AloeVeraZ/TrainUI/Train UI Mini/TrainUIMiniCode/SubwayCatalog.h

#pragma once

#include <Arduino.h>

namespace SubwayCatalog {
struct RouteDef { const char *id; const char *badge; const char *service; const char *feedUrl; const char *aliases; uint16_t stationStart; uint16_t stationCount; };
struct StationDef { const char *id; const char *name; const char *borough; const char *northStop; const char *northLabel; const char *southStop; const char *southLabel; };

static const StationDef STATIONS[] = {
  {"119","103 St","Manhattan","119N","Uptown","119S","Downtown"},
  {"117","116 St-Columbia University","Manhattan","117N","Uptown","117S","Downtown"},
  {"116","125 St","Manhattan","116N","Uptown","116S","Downtown"},
  {"115","137 St-City College","Manhattan","115N","Uptown","115S","Downtown"},
  {"132","14 St","Manhattan","132N","Uptown","132S","Downtown"},
  {"114","145 St","Manhattan","114N","Uptown","114S","Downtown"},
  {"113","157 St","Manhattan","113N","Uptown","113S","Downtown"},
  {"112","168 St-Washington Hts","Manhattan","112N","Uptown","112S","Downtown"},
  {"131","18 St","Manhattan","131N","Uptown","131S","Downtown"},
  {"111","181 St","Manhattan","111N","The Bronx","111S","Downtown"},
  {"110","191 St","Manhattan","110N","The Bronx","110S","Downtown"},
  {"108","207 St","Manhattan","108N","The Bronx","108S","Downtown"},
  {"107","215 St","Manhattan","107N","The Bronx","107S","Downtown"},
  {"130","23 St","Manhattan","130N","Uptown","130S","Downtown"},
  {"104","231 St","Bronx","104N","Van Cortlandt","104S","Manhattan"},
  {"103","238 St","Bronx","103N","Van Cortlandt","103S","Manhattan"},
  {"129","28 St","Manhattan","129N","Uptown","129S","Downtown"},
  {"128","34 St-Penn Station","Manhattan","128N","Uptown","128S","Downtown"},
  {"126","50 St","Manhattan","126N","Uptown","126S","Downtown"},
  {"125","59 St-Columbus Circle","Manhattan","125N","Uptown","125S","Downtown"},
  {"124","66 St-Lincoln Center","Manhattan","124N","Uptown","124S","Downtown"},
  {"123","72 St","Manhattan","123N","Uptown","123S","Downtown"},
  {"122","79 St","Manhattan","122N","Uptown","122S","Downtown"},
  {"121","86 St","Manhattan","121N","Uptown","121S","Downtown"},
  {"120","96 St","Manhattan","120N","Uptown","120S","Downtown"},
  {"135","Canal St","Manhattan","135N","Uptown","135S","Downtown"},
  {"118","Cathedral Pkwy (110 St)","Manhattan","118N","Uptown","118S","Downtown"},
  {"137","Chambers St","Manhattan","137N","Uptown","137S","Downtown"},
  {"133","Christopher St-Stonewall","Manhattan","133N","Uptown","133S","Downtown"},
  {"109","Dyckman St","Manhattan","109N","The Bronx","109S","Downtown"},
  {"136","Franklin St","Manhattan","136N","Uptown","136S","Downtown"},
  {"134","Houston St","Manhattan","134N","Uptown","134S","Downtown"},
  {"106","Marble Hill-225 St","Manhattan","106N","The Bronx","106S","Downtown"},
  {"139","Rector St","Manhattan","139N","Uptown","139S","Downtown"},
  {"142","South Ferry","Manhattan","142N","Uptown","142S","South Ferry"},
  {"127","Times Sq-42 St","Manhattan","127N","Uptown","127S","Downtown"},
  {"101","Van Cortlandt Park-242 St","Bronx","101N","Van Cortlandt Park-242 St","101S","Manhattan"},
  {"138","WTC Cortlandt","Manhattan","138N","Uptown","138S","Downtown"},
  {"227","110 St-Malcolm X Plaza","Manhattan","227N","Uptown","227S","Downtown"},
  {"226","116 St","Manhattan","226N","Uptown","226S","Downtown"},
  {"225","125 St","Manhattan","225N","Uptown","225S","Downtown"},
  {"224","135 St","Manhattan","224N","Uptown","224S","Downtown"},
  {"132","14 St","Manhattan","132N","Uptown","132S","Downtown"},
  {"222","149 St-Hostos","Bronx","222N","Northbound","222S","Manhattan"},
  {"215","174 St","Bronx","215N","Northbound","215S","Manhattan"},
  {"131","18 St","Manhattan","131N","Uptown","131S","Downtown"},
  {"207","219 St","Bronx","207N","Northbound","207S","Manhattan"},
  {"206","225 St","Bronx","206N","Northbound","206S","Manhattan"},
  {"130","23 St","Manhattan","130N","Uptown","130S","Downtown"},
  {"205","233 St","Bronx","205N","Northbound","205S","Manhattan"},
  {"129","28 St","Manhattan","129N","Uptown","129S","Downtown"},
  {"221","3 Av-149 St","Bronx","221N","Northbound","221S","Manhattan"},
  {"128","34 St-Penn Station","Manhattan","128N","Uptown","128S","Downtown"},
  {"126","50 St","Manhattan","126N","Uptown","126S","Downtown"},
  {"125","59 St-Columbus Circle","Manhattan","125N","Uptown","125S","Downtown"},
  {"124","66 St-Lincoln Center","Manhattan","124N","Uptown","124S","Downtown"},
  {"123","72 St","Manhattan","123N","Uptown","123S","Downtown"},
  {"122","79 St","Manhattan","122N","Uptown","122S","Downtown"},
  {"121","86 St","Manhattan","121N","Uptown","121S","Downtown"},
  {"120","96 St","Manhattan","120N","Uptown","120S","Downtown"},
  {"210","Allerton Av","Bronx","210N","Northbound","210S","Manhattan"},
  {"235","Atlantic Av-Barclays Ctr","Brooklyn","235N","Manhattan","235S","Outbound"},
  {"236","Bergen St","Brooklyn","236N","Manhattan","236S","Outbound"},
  {"245","Beverly Rd","Brooklyn","245N","Manhattan","245S","Flatbush"},
  {"232","Borough Hall","Brooklyn","232N","Manhattan","232S","Outbound"},
  {"212","Bronx Park East","Bronx","212N","Northbound","212S","Manhattan"},
  {"209","Burke Av","Bronx","209N","Northbound","209S","Manhattan"},
  {"135","Canal St","Manhattan","135N","Uptown","135S","Downtown"},
  {"137","Chambers St","Manhattan","137N","Uptown","137S","Downtown"},
  {"133","Christopher St-Stonewall","Manhattan","133N","Uptown","133S","Downtown"},
  {"244","Church Av","Brooklyn","244N","Manhattan","244S","Flatbush"},
  {"231","Clark St","Brooklyn","231N","Manhattan","231S","Outbound"},
  {"250","Crown Hts-Utica Av","Brooklyn","250N","Manhattan","250S","Outbound"},
  {"213","E 180 St","Bronx","213N","Northbound","213S","Manhattan"},
  {"238","Eastern Pkwy-Brooklyn Museum","Brooklyn","238N","Manhattan","238S","Outbound"},
  {"247","Flatbush Av-Brooklyn College","Brooklyn","247N","Manhattan","247S","Flatbush Av-Brooklyn College"},
  {"239","Franklin Av-Medgar Evers College","Brooklyn","239N","Manhattan","239S","Outbound"},
  {"136","Franklin St","Manhattan","136N","Uptown","136S","Downtown"},
  {"216","Freeman St","Bronx","216N","Northbound","216S","Manhattan"},
  {"229","Fulton St","Manhattan","229N","Uptown","229S","Brooklyn"},
  {"237","Grand Army Plaza","Brooklyn","237N","Manhattan","237S","Outbound"},
  {"208","Gun Hill Rd","Bronx","208N","Northbound","208S","Manhattan"},
  {"134","Houston St","Manhattan","134N","Uptown","134S","Downtown"},
  {"233","Hoyt St","Brooklyn","233N","Manhattan","233S","Outbound"},
  {"218","Intervale Av","Bronx","218N","Northbound","218S","Manhattan"},
  {"220","Jackson Av","Bronx","220N","Northbound","220S","Manhattan"},
  {"254","Junius St","Brooklyn","254N","Manhattan","254S","New Lots"},
  {"249","Kingston Av","Brooklyn","249N","Manhattan","249S","Outbound"},
  {"204","Nereid Av","Bronx","204N","Northbound","204S","Manhattan"},
  {"234","Nevins St","Brooklyn","234N","Manhattan","234S","Outbound"},
  {"257","New Lots Av","Brooklyn","257N","Manhattan","257S","New Lots Av"},
  {"246","Newkirk Av-Little Haiti","Brooklyn","246N","Manhattan","246S","Flatbush"},
  {"248","Nostrand Av","Brooklyn","248N","Manhattan","248S","Outbound"},
  {"228","Park Place","Manhattan","228N","Uptown","228S","Brooklyn"},
  {"211","Pelham Pkwy","Bronx","211N","Northbound","211S","Manhattan"},
  {"255","Pennsylvania Av","Brooklyn","255N","Manhattan","255S","New Lots"},
  {"241","President St-Medgar Evers College","Brooklyn","241N","Manhattan","241S","Flatbush"},
  {"219","Prospect Av","Bronx","219N","Northbound","219S","Manhattan"},
  {"253","Rockaway Av","Brooklyn","253N","Manhattan","253S","New Lots"},
  {"252","Saratoga Av","Brooklyn","252N","Manhattan","252S","New Lots"},
  {"217","Simpson St","Bronx","217N","Northbound","217S","Manhattan"},
  {"242","Sterling St","Brooklyn","242N","Manhattan","242S","Flatbush"},
  {"251","Sutter Av-Rutland Rd","Brooklyn","251N","Manhattan","251S","New Lots"},
  {"127","Times Sq-42 St","Manhattan","127N","Uptown","127S","Downtown"},
  {"256","Van Siclen Av","Brooklyn","256N","Manhattan","256S","New Lots"},
  {"201","Wakefield-241 St","Bronx","201N","Wakefield-241 St","201S","Manhattan"},
  {"230","Wall St","Manhattan","230N","Uptown","230S","Brooklyn"},
  {"214","West Farms Sq-E Tremont Av","Bronx","214N","Northbound","214S","Manhattan"},
  {"243","Winthrop St","Brooklyn","243N","Manhattan","243S","Flatbush"},
  {"227","110 St-Malcolm X Plaza","Manhattan","227N","Uptown","227S","Downtown"},
  {"226","116 St","Manhattan","226N","Uptown","226S","Downtown"},
  {"225","125 St","Manhattan","225N","Uptown","225S","Downtown"},
  {"224","135 St","Manhattan","224N","Uptown","224S","Downtown"},
  {"132","14 St","Manhattan","132N","Uptown","132S","Downtown"},
  {"302","145 St","Manhattan","302N","Harlem","302S","Downtown"},
  {"128","34 St-Penn Station","Manhattan","128N","Uptown","128S","Downtown"},
  {"123","72 St","Manhattan","123N","Uptown","123S","Downtown"},
  {"120","96 St","Manhattan","120N","Uptown","120S","Downtown"},
  {"235","Atlantic Av-Barclays Ctr","Brooklyn","235N","Manhattan","235S","Outbound"},
  {"236","Bergen St","Brooklyn","236N","Manhattan","236S","Outbound"},
  {"232","Borough Hall","Brooklyn","232N","Manhattan","232S","Outbound"},
  {"137","Chambers St","Manhattan","137N","Uptown","137S","Downtown"},
  {"231","Clark St","Brooklyn","231N","Manhattan","231S","Outbound"},
  {"250","Crown Hts-Utica Av","Brooklyn","250N","Manhattan","250S","Outbound"},
  {"238","Eastern Pkwy-Brooklyn Museum","Brooklyn","238N","Manhattan","238S","Outbound"},
  {"239","Franklin Av-Medgar Evers College","Brooklyn","239N","Manhattan","239S","Outbound"},
  {"229","Fulton St","Manhattan","229N","Uptown","229S","Brooklyn"},
  {"237","Grand Army Plaza","Brooklyn","237N","Manhattan","237S","Outbound"},
  {"301","Harlem-148 St","Manhattan","301N","Harlem-148 St","301S","Downtown"},
  {"233","Hoyt St","Brooklyn","233N","Manhattan","233S","Outbound"},
  {"254","Junius St","Brooklyn","254N","Manhattan","254S","New Lots"},
  {"249","Kingston Av","Brooklyn","249N","Manhattan","249S","Outbound"},
  {"234","Nevins St","Brooklyn","234N","Manhattan","234S","Outbound"},
  {"257","New Lots Av","Brooklyn","257N","Manhattan","257S","New Lots Av"},
  {"248","Nostrand Av","Brooklyn","248N","Manhattan","248S","Outbound"},
  {"228","Park Place","Manhattan","228N","Uptown","228S","Brooklyn"},
  {"255","Pennsylvania Av","Brooklyn","255N","Manhattan","255S","New Lots"},
  {"253","Rockaway Av","Brooklyn","253N","Manhattan","253S","New Lots"},
  {"252","Saratoga Av","Brooklyn","252N","Manhattan","252S","New Lots"},
  {"251","Sutter Av-Rutland Rd","Brooklyn","251N","Manhattan","251S","New Lots"},
  {"127","Times Sq-42 St","Manhattan","127N","Uptown","127S","Downtown"},
  {"256","Van Siclen Av","Brooklyn","256N","Manhattan","256S","New Lots"},
  {"230","Wall St","Manhattan","230N","Uptown","230S","Brooklyn"},
  {"624","103 St","Manhattan","624N","The Bronx","624S","Downtown"},
  {"623","110 St","Manhattan","623N","The Bronx","623S","Downtown"},
  {"622","116 St","Manhattan","622N","The Bronx","622S","Downtown"},
  {"621","125 St","Manhattan","621N","The Bronx","621S","Downtown"},
  {"416","138 St-Grand Concourse","Bronx","416N","Northbound","416S","Manhattan"},
  {"635","14 St-Union Sq","Manhattan","635N","Uptown","635S","Downtown"},
  {"415","149 St-Hostos","Bronx","415N","Northbound","415S","Manhattan"},
  {"414","161 St-Yankee Stadium","Bronx","414N","Northbound","414S","Manhattan"},
  {"413","167 St","Bronx","413N","Northbound","413S","Manhattan"},
  {"412","170 St","Bronx","412N","Northbound","412S","Manhattan"},
  {"410","176 St","Bronx","410N","Northbound","410S","Manhattan"},
  {"408","183 St","Bronx","408N","Northbound","408S","Manhattan"},
  {"634","23 St-Baruch College","Manhattan","634N","Uptown","634S","Downtown"},
  {"633","28 St","Manhattan","633N","Uptown","633S","Downtown"},
  {"632","33 St","Manhattan","632N","Uptown","632S","Downtown"},
  {"630","51 St","Manhattan","630N","Uptown","630S","Downtown"},
  {"629","59 St","Manhattan","629N","Uptown","629S","Downtown"},
  {"628","68 St-Hunter College","Manhattan","628N","Uptown","628S","Downtown"},
  {"627","77 St","Manhattan","627N","Uptown","627S","Downtown"},
  {"626","86 St","Manhattan","626N","Uptown","626S","Downtown"},
  {"625","96 St","Manhattan","625N","The Bronx","625S","Downtown"},
  {"636","Astor Pl","Manhattan","636N","Uptown","636S","Downtown"},
  {"235","Atlantic Av-Barclays Ctr","Brooklyn","235N","Manhattan","235S","Outbound"},
  {"405","Bedford Park Blvd-Lehman College","Bronx","405N","Northbound","405S","Manhattan"},
  {"236","Bergen St","Brooklyn","236N","Manhattan","236S","Outbound"},
  {"637","Bleecker St","Manhattan","637N","Uptown","637S","Downtown"},
  {"423","Borough Hall","Brooklyn","423N","Manhattan","423S","Outbound"},
  {"420","Bowling Green","Manhattan","420N","Uptown","420S","Downtown"},
  {"640","Brooklyn Bridge-City Hall","Manhattan","640N","Uptown","640S","Downtown"},
  {"409","Burnside Av","Bronx","409N","Northbound","409S","Manhattan"},
  {"639","Canal St","Manhattan","639N","Uptown","639S","Downtown"},
  {"250","Crown Hts-Utica Av","Brooklyn","250N","Manhattan","250S","Outbound"},
  {"238","Eastern Pkwy-Brooklyn Museum","Brooklyn","238N","Manhattan","238S","Outbound"},
  {"407","Fordham Rd","Bronx","407N","Northbound","407S","Manhattan"},
  {"239","Franklin Av-Medgar Evers College","Brooklyn","239N","Manhattan","239S","Outbound"},
  {"418","Fulton St","Manhattan","418N","Uptown","418S","Downtown"},
  {"237","Grand Army Plaza","Brooklyn","237N","Manhattan","237S","Outbound"},
  {"631","Grand Central-42 St","Manhattan","631N","Uptown","631S","Downtown"},
  {"254","Junius St","Brooklyn","254N","Manhattan","254S","New Lots"},
  {"406","Kingsbridge Rd","Bronx","406N","Northbound","406S","Manhattan"},
  {"249","Kingston Av","Brooklyn","249N","Manhattan","249S","Outbound"},
  {"402","Mosholu Pkwy","Bronx","402N","Woodlawn","402S","Manhattan"},
  {"411","Mt Eden Av","Bronx","411N","Northbound","411S","Manhattan"},
  {"234","Nevins St","Brooklyn","234N","Manhattan","234S","Outbound"},
  {"257","New Lots Av","Brooklyn","257N","Manhattan","257S","New Lots Av"},
  {"248","Nostrand Av","Brooklyn","248N","Manhattan","248S","Outbound"},
  {"255","Pennsylvania Av","Brooklyn","255N","Manhattan","255S","New Lots"},
  {"253","Rockaway Av","Brooklyn","253N","Manhattan","253S","New Lots"},
  {"252","Saratoga Av","Brooklyn","252N","Manhattan","252S","New Lots"},
  {"638","Spring St","Manhattan","638N","Uptown","638S","Downtown"},
  {"251","Sutter Av-Rutland Rd","Brooklyn","251N","Manhattan","251S","New Lots"},
  {"256","Van Siclen Av","Brooklyn","256N","Manhattan","256S","New Lots"},
  {"419","Wall St","Manhattan","419N","Uptown","419S","Downtown"},
  {"401","Woodlawn","Bronx","401N","Woodlawn","401S","Manhattan"},
  {"621","125 St","Manhattan","621N","The Bronx","621S","Downtown"},
  {"416","138 St-Grand Concourse","Bronx","416N","Northbound","416S","Manhattan"},
  {"635","14 St-Union Sq","Manhattan","635N","Uptown","635S","Downtown"},
  {"222","149 St-Hostos","Bronx","222N","Northbound","222S","Manhattan"},
  {"215","174 St","Bronx","215N","Northbound","215S","Manhattan"},
  {"207","219 St","Bronx","207N","Northbound","207S","Manhattan"},
  {"206","225 St","Bronx","206N","Northbound","206S","Manhattan"},
  {"205","233 St","Bronx","205N","Northbound","205S","Manhattan"},
  {"221","3 Av-149 St","Bronx","221N","Northbound","221S","Manhattan"},
  {"629","59 St","Manhattan","629N","Uptown","629S","Downtown"},
  {"626","86 St","Manhattan","626N","Uptown","626S","Downtown"},
  {"210","Allerton Av","Bronx","210N","Northbound","210S","Manhattan"},
  {"235","Atlantic Av-Barclays Ctr","Brooklyn","235N","Manhattan","235S","Outbound"},
  {"502","Baychester Av","Bronx","502N","Eastchester","502S","Manhattan"},
  {"245","Beverly Rd","Brooklyn","245N","Manhattan","245S","Flatbush"},
  {"423","Borough Hall","Brooklyn","423N","Manhattan","423S","Outbound"},
  {"420","Bowling Green","Manhattan","420N","Uptown","420S","Downtown"},
  {"212","Bronx Park East","Bronx","212N","Northbound","212S","Manhattan"},
  {"640","Brooklyn Bridge-City Hall","Manhattan","640N","Uptown","640S","Downtown"},
  {"209","Burke Av","Bronx","209N","Northbound","209S","Manhattan"},
  {"244","Church Av","Brooklyn","244N","Manhattan","244S","Flatbush"},
  {"250","Crown Hts-Utica Av","Brooklyn","250N","Manhattan","250S","Outbound"},
  {"213","E 180 St","Bronx","213N","Northbound","213S","Manhattan"},
  {"501","Eastchester-Dyre Av","Bronx","501N","Eastchester-Dyre Av","501S","Manhattan"},
  {"247","Flatbush Av-Brooklyn College","Brooklyn","247N","Manhattan","247S","Flatbush Av-Brooklyn College"},
  {"239","Franklin Av-Medgar Evers College","Brooklyn","239N","Manhattan","239S","Outbound"},
  {"216","Freeman St","Bronx","216N","Northbound","216S","Manhattan"},
  {"418","Fulton St","Manhattan","418N","Uptown","418S","Downtown"},
  {"631","Grand Central-42 St","Manhattan","631N","Uptown","631S","Downtown"},
  {"208","Gun Hill Rd","Bronx","208N","Northbound","208S","Manhattan"},
  {"503","Gun Hill Rd","Bronx","503N","Eastchester","503S","Manhattan"},
  {"218","Intervale Av","Bronx","218N","Northbound","218S","Manhattan"},
  {"220","Jackson Av","Bronx","220N","Northbound","220S","Manhattan"},
  {"254","Junius St","Brooklyn","254N","Manhattan","254S","New Lots"},
  {"249","Kingston Av","Brooklyn","249N","Manhattan","249S","Outbound"},
  {"505","Morris Park","Bronx","505N","Eastchester","505S","Manhattan"},
  {"204","Nereid Av","Bronx","204N","Northbound","204S","Manhattan"},
  {"234","Nevins St","Brooklyn","234N","Manhattan","234S","Outbound"},
  {"257","New Lots Av","Brooklyn","257N","Manhattan","257S","New Lots Av"},
  {"246","Newkirk Av-Little Haiti","Brooklyn","246N","Manhattan","246S","Flatbush"},
  {"248","Nostrand Av","Brooklyn","248N","Manhattan","248S","Outbound"},
  {"211","Pelham Pkwy","Bronx","211N","Northbound","211S","Manhattan"},
  {"504","Pelham Pkwy","Bronx","504N","Eastchester","504S","Manhattan"},
  {"255","Pennsylvania Av","Brooklyn","255N","Manhattan","255S","New Lots"},
  {"241","President St-Medgar Evers College","Brooklyn","241N","Manhattan","241S","Flatbush"},
  {"219","Prospect Av","Bronx","219N","Northbound","219S","Manhattan"},
  {"253","Rockaway Av","Brooklyn","253N","Manhattan","253S","New Lots"},
  {"252","Saratoga Av","Brooklyn","252N","Manhattan","252S","New Lots"},
  {"217","Simpson St","Bronx","217N","Northbound","217S","Manhattan"},
  {"242","Sterling St","Brooklyn","242N","Manhattan","242S","Flatbush"},
  {"251","Sutter Av-Rutland Rd","Brooklyn","251N","Manhattan","251S","New Lots"},
  {"256","Van Siclen Av","Brooklyn","256N","Manhattan","256S","New Lots"},
  {"419","Wall St","Manhattan","419N","Uptown","419S","Downtown"},
  {"214","West Farms Sq-E Tremont Av","Bronx","214N","Northbound","214S","Manhattan"},
  {"243","Winthrop St","Brooklyn","243N","Manhattan","243S","Flatbush"},
  {"624","103 St","Manhattan","624N","The Bronx","624S","Downtown"},
  {"623","110 St","Manhattan","623N","The Bronx","623S","Downtown"},
  {"622","116 St","Manhattan","622N","The Bronx","622S","Downtown"},
  {"621","125 St","Manhattan","621N","The Bronx","621S","Downtown"},
  {"635","14 St-Union Sq","Manhattan","635N","Uptown","635S","Downtown"},
  {"634","23 St-Baruch College","Manhattan","634N","Uptown","634S","Downtown"},
  {"633","28 St","Manhattan","633N","Uptown","633S","Downtown"},
  {"619","3 Av-138 St","Bronx","619N","Northbound","619S","Manhattan"},
  {"632","33 St","Manhattan","632N","Uptown","632S","Downtown"},
  {"630","51 St","Manhattan","630N","Uptown","630S","Downtown"},
  {"629","59 St","Manhattan","629N","Uptown","629S","Downtown"},
  {"628","68 St-Hunter College","Manhattan","628N","Uptown","628S","Downtown"},
  {"627","77 St","Manhattan","627N","Uptown","627S","Downtown"},
  {"626","86 St","Manhattan","626N","Uptown","626S","Downtown"},
  {"625","96 St","Manhattan","625N","The Bronx","625S","Downtown"},
  {"636","Astor Pl","Manhattan","636N","Uptown","636S","Downtown"},
  {"637","Bleecker St","Manhattan","637N","Uptown","637S","Downtown"},
  {"618","Brook Av","Bronx","618N","Northbound","618S","Manhattan"},
  {"640","Brooklyn Bridge-City Hall","Manhattan","640N","Uptown","640S","Downtown"},
  {"602","Buhre Av","Bronx","602N","Pelham Bay","602S","Manhattan"},
  {"639","Canal St","Manhattan","639N","Uptown","639S","Downtown"},
  {"607","Castle Hill Av","Bronx","607N","Pelham Bay","607S","Manhattan"},
  {"617","Cypress Av","Bronx","617N","Northbound","617S","Manhattan"},
  {"616","E 143 St-St Mary's St","Bronx","616N","Northbound","616S","Manhattan"},
  {"615","E 149 St","Bronx","615N","Northbound","615S","Manhattan"},
  {"611","Elder Av","Bronx","611N","Northbound","611S","Manhattan"},
  {"631","Grand Central-42 St","Manhattan","631N","Uptown","631S","Downtown"},
  {"613","Hunts Point Av","Bronx","613N","Northbound","613S","Manhattan"},
  {"614","Longwood Av","Bronx","614N","Northbound","614S","Manhattan"},
  {"603","Middletown Rd","Bronx","603N","Pelham Bay","603S","Manhattan"},
  {"610","Morrison Av-Soundview","Bronx","610N","Northbound","610S","Manhattan"},
  {"608","Parkchester","Bronx","608N","Northbound","608S","Manhattan"},
  {"601","Pelham Bay Park","Bronx","601N","Pelham Bay Park","601S","Manhattan"},
  {"638","Spring St","Manhattan","638N","Uptown","638S","Downtown"},
  {"609","St Lawrence Av","Bronx","609N","Northbound","609S","Manhattan"},
  {"604","Westchester Sq-E Tremont Av","Bronx","604N","Pelham Bay","604S","Manhattan"},
  {"612","Whitlock Av","Bronx","612N","Northbound","612S","Manhattan"},
  {"606","Zerega Av","Bronx","606N","Pelham Bay","606S","Manhattan"},
  {"706","103 St-Corona Plaza","Queens","706N","Outbound","706S","Manhattan"},
  {"705","111 St","Queens","705N","Outbound","705S","Manhattan"},
  {"716","33 St-Rawson St","Queens","716N","Outbound","716S","Manhattan"},
  {"726","34 St-Hudson Yards","Manhattan","726N","Flushing-Main St","726S","Queens"},
  {"715","40 St-Lowery St","Queens","715N","Outbound","715S","Manhattan"},
  {"714","46 St-Bliss St","Queens","714N","Outbound","714S","Manhattan"},
  {"724","5 Av","Manhattan","724N","Queens","724S","Hudson Yards"},
  {"713","52 St","Queens","713N","Outbound","713S","Manhattan"},
  {"712","61 St-Woodside","Queens","712N","Outbound","712S","Manhattan"},
  {"711","69 St","Queens","711N","Outbound","711S","Manhattan"},
  {"710","74 St-Broadway","Queens","710N","Outbound","710S","Manhattan"},
  {"709","82 St-Jackson Hts","Queens","709N","Outbound","709S","Manhattan"},
  {"708","90 St-Elmhurst Av","Queens","708N","Outbound","708S","Manhattan"},
  {"719","Court Sq","Queens","719N","Outbound","719S","Manhattan"},
  {"701","Flushing-Main St","Queens","701N","Flushing-Main St","701S","Manhattan"},
  {"723","Grand Central-42 St","Manhattan","723N","Queens","723S","Hudson Yards"},
  {"720","Hunters Point Av","Queens","720N","Outbound","720S","Manhattan"},
  {"707","Junction Blvd","Queens","707N","Outbound","707S","Manhattan"},
  {"702","Mets-Willets Point","Queens","702N","Outbound","702S","Manhattan"},
  {"718","Queensboro Plaza","Queens","718N","Outbound","718S","Manhattan"},
  {"725","Times Sq-42 St","Manhattan","725N","Queens","725S","Hudson Yards"},
  {"721","Vernon Blvd-Jackson Av","Queens","721N","Outbound","721S","Manhattan"},
  {"A18","103 St","Manhattan","A18N","Uptown","A18S","Downtown"},
  {"A63","104 St","Queens","A63N","Manhattan","A63S","Ozone Park"},
  {"A64","111 St","Queens","A64N","Manhattan","A64S","Ozone Park"},
  {"A16","116 St","Manhattan","A16N","Uptown","A16S","Downtown"},
  {"A15","125 St","Manhattan","A15N","Uptown","A15S","Downtown"},
  {"A14","135 St","Manhattan","A14N","Uptown","A14S","Downtown"},
  {"A31","14 St","Manhattan","A31N","Uptown","A31S","Downtown"},
  {"A12","145 St","Manhattan","A12N","Uptown","A12S","Downtown"},
  {"A11","155 St","Manhattan","A11N","Uptown","A11S","Downtown"},
  {"A10","163 St-Amsterdam Av","Manhattan","A10N","Uptown","A10S","Downtown"},
  {"A09","168 St","Manhattan","A09N","Uptown","A09S","Downtown"},
  {"A07","175 St","Manhattan","A07N","Uptown","A07S","Downtown"},
  {"A06","181 St","Manhattan","A06N","Uptown","A06S","Downtown"},
  {"A05","190 St","Manhattan","A05N","Uptown","A05S","Downtown"},
  {"A30","23 St","Manhattan","A30N","Uptown","A30S","Downtown"},
  {"A28","34 St-Penn Station","Manhattan","A28N","Uptown","A28S","Downtown"},
  {"A27","42 St-Port Authority Bus Terminal","Manhattan","A27N","Uptown","A27S","Downtown"},
  {"A25","50 St","Manhattan","A25N","Uptown","A25S","Downtown"},
  {"A24","59 St-Columbus Circle","Manhattan","A24N","Uptown","A24S","Downtown"},
  {"A22","72 St","Manhattan","A22N","Uptown","A22S","Downtown"},
  {"A59","80 St","Queens","A59N","Manhattan","A59S","Outbound"},
  {"A21","81 St-Museum of Natural History","Manhattan","A21N","Uptown","A21S","Downtown"},
  {"A20","86 St","Manhattan","A20N","Uptown","A20S","Downtown"},
  {"A60","88 St","Queens","A60N","Manhattan","A60S","Outbound"},
  {"A19","96 St","Manhattan","A19N","Uptown","A19S","Downtown"},
  {"H01","Aqueduct Racetrack","Queens","H01N","Manhattan","H01S","Rockaways"},
  {"H02","Aqueduct-N Conduit Av","Queens","H02N","Manhattan","H02S","Rockaways"},
  {"H14","Beach 105 St","Queens","H14N","Inbound","H14S","Rockaway Park"},
  {"H10","Beach 25 St","Queens","H10N","Manhattan","H10S","Far Rockaway"},
  {"H09","Beach 36 St","Queens","H09N","Manhattan","H09S","Far Rockaway"},
  {"H08","Beach 44 St","Queens","H08N","Manhattan","H08S","Far Rockaway"},
  {"H07","Beach 60 St","Queens","H07N","Manhattan","H07S","Far Rockaway"},
  {"H06","Beach 67 St","Queens","H06N","Manhattan","H06S","Far Rockaway"},
  {"H12","Beach 90 St","Queens","H12N","Inbound","H12S","Rockaway Park"},
  {"H13","Beach 98 St","Queens","H13N","Inbound","H13S","Rockaway Park"},
  {"H04","Broad Channel","Queens","H04N","Inbound","H04S","Rockaways"},
  {"A51","Broadway Junction","Brooklyn","A51N","Manhattan","A51S","Outbound"},
  {"A34","Canal St","Manhattan","A34N","Uptown","A34S","Downtown"},
  {"A17","Cathedral Pkwy (110 St)","Manhattan","A17N","Uptown","A17S","Downtown"},
  {"A36","Chambers St","Manhattan","A36N","Uptown","A36S","Brooklyn"},
  {"A44","Clinton-Washington Avs","Brooklyn","A44N","Manhattan","A44S","Outbound"},
  {"A03","Dyckman St","Manhattan","A03N","Uptown","A03S","Downtown"},
  {"A55","Euclid Av","Brooklyn","A55N","Manhattan","A55S","Queens"},
  {"H11","Far Rockaway-Mott Av","Queens","H11N","Manhattan","H11S","Far Rockaway-Mott Av"},
  {"A45","Franklin Av","Brooklyn","A45N","Manhattan","A45S","Outbound"},
  {"A38","Fulton St","Manhattan","A38N","Uptown","A38S","Brooklyn"},
  {"A57","Grant Av","Brooklyn","A57N","Manhattan","A57S","Queens"},
  {"A40","High St","Brooklyn","A40N","Manhattan","A40S","Outbound"},
  {"H03","Howard Beach-JFK Airport","Queens","H03N","Manhattan","H03S","Rockaways"},
  {"A42","Hoyt-Schermerhorn Sts","Brooklyn","A42N","Westbound","A42S","Queens"},
  {"A02","Inwood-207 St","Manhattan","A02N","Inwood-207 St","A02S","Downtown"},
  {"A41","Jay St-MetroTech","Brooklyn","A41N","Manhattan","A41S","Outbound"},
  {"A47","Kingston-Throop Avs","Brooklyn","A47N","Manhattan","A47S","Outbound"},
  {"A43","Lafayette Av","Brooklyn","A43N","Manhattan","A43S","Outbound"},
  {"A52","Liberty Av","Brooklyn","A52N","Manhattan","A52S","Outbound"},
  {"A46","Nostrand Av","Brooklyn","A46N","Manhattan","A46S","Outbound"},
  {"A65","Ozone Park-Lefferts Blvd","Queens","A65N","Manhattan","A65S","Ozone Park-Lefferts Blvd"},
  {"A49","Ralph Av","Brooklyn","A49N","Manhattan","A49S","Outbound"},
  {"A50","Rockaway Av","Brooklyn","A50N","Manhattan","A50S","Outbound"},
  {"A61","Rockaway Blvd","Queens","A61N","Manhattan","A61S","Outbound"},
  {"H15","Rockaway Park-Beach 116 St","Queens","H15N","Inbound","H15S","Rockaway Park-Beach 116 St"},
  {"A54","Shepherd Av","Brooklyn","A54N","Manhattan","A54S","Outbound"},
  {"A33","Spring St","Manhattan","A33N","Uptown","A33S","Downtown"},
  {"A48","Utica Av","Brooklyn","A48N","Manhattan","A48S","Outbound"},
  {"A53","Van Siclen Av","Brooklyn","A53N","Manhattan","A53S","Outbound"},
  {"A32","W 4 St-Wash Sq","Manhattan","A32N","Uptown","A32S","Downtown"},
  {"A18","103 St","Manhattan","A18N","Uptown","A18S","Downtown"},
  {"A16","116 St","Manhattan","A16N","Uptown","A16S","Downtown"},
  {"A15","125 St","Manhattan","A15N","Uptown","A15S","Downtown"},
  {"A14","135 St","Manhattan","A14N","Uptown","A14S","Downtown"},
  {"A31","14 St","Manhattan","A31N","Uptown","A31S","Downtown"},
  {"A12","145 St","Manhattan","A12N","Uptown","A12S","Downtown"},
  {"A11","155 St","Manhattan","A11N","Uptown","A11S","Downtown"},
  {"A10","163 St-Amsterdam Av","Manhattan","A10N","Uptown","A10S","Downtown"},
  {"A09","168 St","Manhattan","A09N","Uptown","A09S","Downtown"},
  {"A30","23 St","Manhattan","A30N","Uptown","A30S","Downtown"},
  {"A28","34 St-Penn Station","Manhattan","A28N","Uptown","A28S","Downtown"},
  {"A27","42 St-Port Authority Bus Terminal","Manhattan","A27N","Uptown","A27S","Downtown"},
  {"A25","50 St","Manhattan","A25N","Uptown","A25S","Downtown"},
  {"A24","59 St-Columbus Circle","Manhattan","A24N","Uptown","A24S","Downtown"},
  {"A22","72 St","Manhattan","A22N","Uptown","A22S","Downtown"},
  {"A21","81 St-Museum of Natural History","Manhattan","A21N","Uptown","A21S","Downtown"},
  {"A20","86 St","Manhattan","A20N","Uptown","A20S","Downtown"},
  {"A19","96 St","Manhattan","A19N","Uptown","A19S","Downtown"},
  {"A51","Broadway Junction","Brooklyn","A51N","Manhattan","A51S","Outbound"},
  {"A34","Canal St","Manhattan","A34N","Uptown","A34S","Downtown"},
  {"A17","Cathedral Pkwy (110 St)","Manhattan","A17N","Uptown","A17S","Downtown"},
  {"A36","Chambers St","Manhattan","A36N","Uptown","A36S","Brooklyn"},
  {"A44","Clinton-Washington Avs","Brooklyn","A44N","Manhattan","A44S","Outbound"},
  {"A55","Euclid Av","Brooklyn","A55N","Manhattan","A55S","Queens"},
  {"A45","Franklin Av","Brooklyn","A45N","Manhattan","A45S","Outbound"},
  {"A38","Fulton St","Manhattan","A38N","Uptown","A38S","Brooklyn"},
  {"A40","High St","Brooklyn","A40N","Manhattan","A40S","Outbound"},
  {"A42","Hoyt-Schermerhorn Sts","Brooklyn","A42N","Westbound","A42S","Queens"},
  {"A41","Jay St-MetroTech","Brooklyn","A41N","Manhattan","A41S","Outbound"},
  {"A47","Kingston-Throop Avs","Brooklyn","A47N","Manhattan","A47S","Outbound"},
  {"A43","Lafayette Av","Brooklyn","A43N","Manhattan","A43S","Outbound"},
  {"A52","Liberty Av","Brooklyn","A52N","Manhattan","A52S","Outbound"},
  {"A46","Nostrand Av","Brooklyn","A46N","Manhattan","A46S","Outbound"},
  {"A49","Ralph Av","Brooklyn","A49N","Manhattan","A49S","Outbound"},
  {"A50","Rockaway Av","Brooklyn","A50N","Manhattan","A50S","Outbound"},
  {"A54","Shepherd Av","Brooklyn","A54N","Manhattan","A54S","Outbound"},
  {"A33","Spring St","Manhattan","A33N","Uptown","A33S","Downtown"},
  {"A48","Utica Av","Brooklyn","A48N","Manhattan","A48S","Outbound"},
  {"A53","Van Siclen Av","Brooklyn","A53N","Manhattan","A53S","Outbound"},
  {"A32","W 4 St-Wash Sq","Manhattan","A32N","Uptown","A32S","Downtown"},
  {"A31","14 St","Manhattan","A31N","Uptown","A31S","Downtown"},
  {"F02","169 St","Queens","F02N","Jamaica","F02S","Manhattan"},
  {"A30","23 St","Manhattan","A30N","Uptown","A30S","Downtown"},
  {"A28","34 St-Penn Station","Manhattan","A28N","Uptown","A28S","Downtown"},
  {"G20","36 St","Queens","G20N","Outbound","G20S","Manhattan"},
  {"A27","42 St-Port Authority Bus Terminal","Manhattan","A27N","Uptown","A27S","Downtown"},
  {"G18","46 St","Queens","G18N","Outbound","G18S","Manhattan"},
  {"F12","5 Av/53 St","Manhattan","F12N","Queens","F12S","Downtown"},
  {"A25","50 St","Manhattan","A25N","Uptown","A25S","Downtown"},
  {"G10","63 Dr-Rego Park","Queens","G10N","Outbound","G10S","Manhattan"},
  {"G15","65 St","Queens","G15N","Outbound","G15S","Manhattan"},
  {"G09","67 Av","Queens","G09N","Outbound","G09S","Manhattan"},
  {"D14","7 Av","Manhattan","D14N","Outbound","D14S","Downtown"},
  {"F07","75 Av","Queens","F07N","Jamaica","F07S","Manhattan"},
  {"F05","Briarwood","Queens","F05N","Jamaica","F05S","Manhattan"},
  {"A34","Canal St","Manhattan","A34N","Uptown","A34S","Downtown"},
  {"F09","Court Sq-23 St","Queens","F09N","Outbound","F09S","Manhattan"},
  {"G13","Elmhurst Av","Queens","G13N","Outbound","G13S","Manhattan"},
  {"G08","Forest Hills-71 Av","Queens","G08N","Outbound","G08S","Manhattan"},
  {"G12","Grand Av-Newtown","Queens","G12N","Outbound","G12S","Manhattan"},
  {"G14","Jackson Hts-Roosevelt Av","Queens","G14N","Outbound","G14S","Manhattan"},
  {"G05","Jamaica Center-Parsons/Archer","Queens","G05N","Jamaica Center-Parsons/Archer","G05S","Manhattan"},
  {"F01","Jamaica-179 St","Queens","F01N","Jamaica-179 St","F01S","Manhattan"},
  {"G07","Jamaica-Van Wyck","Queens","G07N","Jamaica","G07S","Manhattan"},
  {"F06","Kew Gardens-Union Tpke","Queens","F06N","Jamaica","F06S","Manhattan"},
  {"F11","Lexington Av/53 St","Manhattan","F11N","Queens","F11S","Downtown"},
  {"G16","Northern Blvd","Queens","G16N","Outbound","G16S","Manhattan"},
  {"F03","Parsons Blvd","Queens","F03N","Jamaica","F03S","Manhattan"},
  {"G21","Queens Plaza","Queens","G21N","Outbound","G21S","Manhattan"},
  {"A33","Spring St","Manhattan","A33N","Uptown","A33S","Downtown"},
  {"G19","Steinway St","Queens","G19N","Outbound","G19S","Manhattan"},
  {"F04","Sutphin Blvd","Queens","F04N","Jamaica","F04S","Manhattan"},
  {"G06","Sutphin Blvd-Archer Av-JFK Airport","Queens","G06N","Jamaica","G06S","Manhattan"},
  {"A32","W 4 St-Wash Sq","Manhattan","A32N","Uptown","A32S","Downtown"},
  {"G11","Woodhaven Blvd","Queens","G11N","Outbound","G11S","Manhattan"},
  {"E01","World Trade Center","Manhattan","E01N","Uptown","E01S","World Trade Center"},
  {"A18","103 St","Manhattan","A18N","Uptown","A18S","Downtown"},
  {"A16","116 St","Manhattan","A16N","Uptown","A16S","Downtown"},
  {"A15","125 St","Manhattan","A15N","Uptown","A15S","Downtown"},
  {"A14","135 St","Manhattan","A14N","Uptown","A14S","Downtown"},
  {"D13","145 St","Manhattan","D13N","Uptown","D13S","Downtown"},
  {"D12","155 St","Manhattan","D12N","The Bronx","D12S","Downtown"},
  {"D11","161 St-Yankee Stadium","Bronx","D11N","Northbound","D11S","Manhattan"},
  {"D10","167 St","Bronx","D10N","Northbound","D10S","Manhattan"},
  {"D09","170 St","Bronx","D09N","Northbound","D09S","Manhattan"},
  {"D08","174-175 Sts","Bronx","D08N","Northbound","D08S","Manhattan"},
  {"D06","182-183 Sts","Bronx","D06N","Northbound","D06S","Manhattan"},
  {"D17","34 St-Herald Sq","Manhattan","D17N","Uptown","D17S","Downtown"},
  {"D16","42 St-Bryant Pk","Manhattan","D16N","Uptown","D16S","Downtown"},
  {"D15","47-50 Sts-Rockefeller Ctr","Manhattan","D15N","Uptown","D15S","Downtown"},
  {"A24","59 St-Columbus Circle","Manhattan","A24N","Uptown","A24S","Downtown"},
  {"D14","7 Av","Manhattan","D14N","Outbound","D14S","Downtown"},
  {"D25","7 Av","Brooklyn","D25N","Manhattan","D25S","Southbound"},
  {"A22","72 St","Manhattan","A22N","Uptown","A22S","Downtown"},
  {"A21","81 St-Museum of Natural History","Manhattan","A21N","Uptown","A21S","Downtown"},
  {"A20","86 St","Manhattan","A20N","Uptown","A20S","Downtown"},
  {"A19","96 St","Manhattan","A19N","Uptown","A19S","Downtown"},
  {"D24","Atlantic Av-Barclays Ctr","Brooklyn","D24N","Manhattan","D24S","Southbound"},
  {"D03","Bedford Park Blvd","Bronx","D03N","Northbound","D03S","Manhattan"},
  {"D40","Brighton Beach","Brooklyn","D40N","Manhattan","D40S","Southbound"},
  {"D21","Broadway-Lafayette St","Manhattan","D21N","Uptown","D21S","Downtown"},
  {"A17","Cathedral Pkwy (110 St)","Manhattan","A17N","Uptown","A17S","Downtown"},
  {"D28","Church Av","Brooklyn","D28N","Manhattan","D28S","Southbound"},
  {"R30","DeKalb Av","Brooklyn","R30N","Manhattan","R30S","Southbound"},
  {"D05","Fordham Rd","Bronx","D05N","Northbound","D05S","Manhattan"},
  {"D22","Grand St","Manhattan","D22N","Uptown","D22S","Brooklyn"},
  {"D35","Kings Hwy","Brooklyn","D35N","Manhattan","D35S","Southbound"},
  {"D04","Kingsbridge Rd","Bronx","D04N","Northbound","D04S","Manhattan"},
  {"D31","Newkirk Plaza","Brooklyn","D31N","Manhattan","D31S","Southbound"},
  {"D26","Prospect Park","Brooklyn","D26N","Northbound","D26S","Southbound"},
  {"D39","Sheepshead Bay","Brooklyn","D39N","Manhattan","D39S","Southbound"},
  {"D07","Tremont Av","Bronx","D07N","Northbound","D07S","Manhattan"},
  {"D20","W 4 St-Wash Sq","Manhattan","D20N","Uptown","D20S","Downtown"},
  {"A15","125 St","Manhattan","A15N","Uptown","A15S","Downtown"},
  {"D13","145 St","Manhattan","D13N","Uptown","D13S","Downtown"},
  {"D12","155 St","Manhattan","D12N","The Bronx","D12S","Downtown"},
  {"D11","161 St-Yankee Stadium","Bronx","D11N","Northbound","D11S","Manhattan"},
  {"D10","167 St","Bronx","D10N","Northbound","D10S","Manhattan"},
  {"D09","170 St","Bronx","D09N","Northbound","D09S","Manhattan"},
  {"D08","174-175 Sts","Bronx","D08N","Northbound","D08S","Manhattan"},
  {"B19","18 Av","Brooklyn","B19N","Manhattan","B19S","Southbound"},
  {"D06","182-183 Sts","Bronx","D06N","Northbound","D06S","Manhattan"},
  {"B20","20 Av","Brooklyn","B20N","Manhattan","B20S","Southbound"},
  {"B22","25 Av","Brooklyn","B22N","Manhattan","B22S","Coney Island"},
  {"R35","25 St","Brooklyn","R35N","Manhattan","R35S","Southbound"},
  {"D17","34 St-Herald Sq","Manhattan","D17N","Uptown","D17S","Downtown"},
  {"R36","36 St","Brooklyn","R36N","Manhattan","R36S","Southbound"},
  {"R33","4 Av-9 St","Brooklyn","R33N","Manhattan","R33S","Southbound"},
  {"D16","42 St-Bryant Pk","Manhattan","D16N","Uptown","D16S","Downtown"},
  {"D15","47-50 Sts-Rockefeller Ctr","Manhattan","D15N","Uptown","D15S","Downtown"},
  {"B14","50 St","Brooklyn","B14N","Manhattan","B14S","Southbound"},
  {"B15","55 St","Brooklyn","B15N","Manhattan","B15S","Southbound"},
  {"A24","59 St-Columbus Circle","Manhattan","A24N","Uptown","A24S","Downtown"},
  {"B16","62 St","Brooklyn","B16N","Manhattan","B16S","Southbound"},
  {"D14","7 Av","Manhattan","D14N","Outbound","D14S","Downtown"},
  {"B17","71 St","Brooklyn","B17N","Manhattan","B17S","Southbound"},
  {"B18","79 St","Brooklyn","B18N","Manhattan","B18S","Southbound"},
  {"B12","9 Av","Brooklyn","B12N","Manhattan","B12S","Southbound"},
  {"R31","Atlantic Av-Barclays Ctr","Brooklyn","R31N","Manhattan","R31S","Southbound"},
  {"B23","Bay 50 St","Brooklyn","B23N","Manhattan","B23S","Coney Island"},
  {"B21","Bay Pkwy","Brooklyn","B21N","Manhattan","B21S","Southbound"},
  {"D03","Bedford Park Blvd","Bronx","D03N","Northbound","D03S","Manhattan"},
  {"D21","Broadway-Lafayette St","Manhattan","D21N","Uptown","D21S","Downtown"},
  {"D43","Coney Island-Stillwell Av","Brooklyn","D43N","Manhattan","D43S","Coney Island-Stillwell Av"},
  {"R30","DeKalb Av","Brooklyn","R30N","Manhattan","R30S","Southbound"},
  {"D05","Fordham Rd","Bronx","D05N","Northbound","D05S","Manhattan"},
  {"B13","Fort Hamilton Pkwy","Brooklyn","B13N","Manhattan","B13S","Southbound"},
  {"D22","Grand St","Manhattan","D22N","Uptown","D22S","Brooklyn"},
  {"D04","Kingsbridge Rd","Bronx","D04N","Northbound","D04S","Manhattan"},
  {"D01","Norwood-205 St","Bronx","D01N","Norwood-205 St","D01S","Manhattan"},
  {"R34","Prospect Av","Brooklyn","R34N","Manhattan","R34S","Southbound"},
  {"D07","Tremont Av","Bronx","D07N","Northbound","D07S","Manhattan"},
  {"R32","Union St","Brooklyn","R32N","Manhattan","R32S","Southbound"},
  {"D20","W 4 St-Wash Sq","Manhattan","D20N","Uptown","D20S","Downtown"},
  {"D19","14 St","Manhattan","D19N","Uptown","D19S","Downtown"},
  {"F25","15 St-Prospect Park","Brooklyn","F25N","Northbound","F25S","Southbound"},
  {"F02","169 St","Queens","F02N","Jamaica","F02S","Manhattan"},
  {"F30","18 Av","Brooklyn","F30N","Manhattan","F30S","Southbound"},
  {"F14","2 Av","Manhattan","F14N","Uptown","F14S","Downtown"},
  {"B04","21 St-Queensbridge","Queens","B04N","Outbound","B04S","Manhattan"},
  {"D18","23 St","Manhattan","D18N","Uptown","D18S","Downtown"},
  {"D17","34 St-Herald Sq","Manhattan","D17N","Uptown","D17S","Downtown"},
  {"G20","36 St","Queens","G20N","Outbound","G20S","Manhattan"},
  {"F23","4 Av-9 St","Brooklyn","F23N","Northbound","F23S","Southbound"},
  {"D16","42 St-Bryant Pk","Manhattan","D16N","Uptown","D16S","Downtown"},
  {"G18","46 St","Queens","G18N","Outbound","G18S","Manhattan"},
  {"D15","47-50 Sts-Rockefeller Ctr","Manhattan","D15N","Uptown","D15S","Downtown"},
  {"F12","5 Av/53 St","Manhattan","F12N","Queens","F12S","Downtown"},
  {"B10","57 St","Manhattan","B10N","Uptown","B10S","Downtown"},
  {"G10","63 Dr-Rego Park","Queens","G10N","Outbound","G10S","Manhattan"},
  {"G15","65 St","Queens","G15N","Outbound","G15S","Manhattan"},
  {"G09","67 Av","Queens","G09N","Outbound","G09S","Manhattan"},
  {"F24","7 Av","Brooklyn","F24N","Northbound","F24S","Southbound"},
  {"F07","75 Av","Queens","F07N","Jamaica","F07S","Manhattan"},
  {"F31","Avenue I","Brooklyn","F31N","Manhattan","F31S","Southbound"},
  {"F33","Avenue N","Brooklyn","F33N","Manhattan","F33S","Southbound"},
  {"F34","Avenue P","Brooklyn","F34N","Manhattan","F34S","Southbound"},
  {"F36","Avenue U","Brooklyn","F36N","Manhattan","F36S","Coney Island"},
  {"F38","Avenue X","Brooklyn","F38N","Manhattan","F38S","Coney Island"},
  {"F32","Bay Pkwy","Brooklyn","F32N","Manhattan","F32S","Southbound"},
  {"F20","Bergen St","Brooklyn","F20N","Northbound","F20S","Southbound"},
  {"F05","Briarwood","Queens","F05N","Jamaica","F05S","Manhattan"},
  {"D21","Broadway-Lafayette St","Manhattan","D21N","Uptown","D21S","Downtown"},
  {"F21","Carroll St","Brooklyn","F21N","Northbound","F21S","Southbound"},
  {"F27","Church Av","Brooklyn","F27N","Northbound","F27S","Southbound"},
  {"D43","Coney Island-Stillwell Av","Brooklyn","D43N","Manhattan","D43S","Coney Island-Stillwell Av"},
  {"F09","Court Sq-23 St","Queens","F09N","Outbound","F09S","Manhattan"},
  {"F15","Delancey St-Essex St","Manhattan","F15N","Uptown","F15S","Brooklyn"},
  {"F29","Ditmas Av","Brooklyn","F29N","Manhattan","F29S","Southbound"},
  {"F16","East Broadway","Manhattan","F16N","Uptown","F16S","Brooklyn"},
  {"G13","Elmhurst Av","Queens","G13N","Outbound","G13S","Manhattan"},
  {"G08","Forest Hills-71 Av","Queens","G08N","Outbound","G08S","Manhattan"},
  {"F26","Fort Hamilton Pkwy","Brooklyn","F26N","Northbound","F26S","Southbound"},
  {"G12","Grand Av-Newtown","Queens","G12N","Outbound","G12S","Manhattan"},
  {"G14","Jackson Hts-Roosevelt Av","Queens","G14N","Outbound","G14S","Manhattan"},
  {"F01","Jamaica-179 St","Queens","F01N","Jamaica-179 St","F01S","Manhattan"},
  {"A41","Jay St-MetroTech","Brooklyn","A41N","Manhattan","A41S","Outbound"},
  {"F06","Kew Gardens-Union Tpke","Queens","F06N","Jamaica","F06S","Manhattan"},
  {"F35","Kings Hwy","Brooklyn","F35N","Manhattan","F35S","Southbound"},
  {"F11","Lexington Av/53 St","Manhattan","F11N","Queens","F11S","Downtown"},
  {"B08","Lexington Av/63 St","Manhattan","B08N","Uptown & Queens","B08S","Downtown"},
  {"F39","Neptune Av","Brooklyn","F39N","Manhattan","F39S","Coney Island"},
  {"G16","Northern Blvd","Queens","G16N","Outbound","G16S","Manhattan"},
  {"F03","Parsons Blvd","Queens","F03N","Jamaica","F03S","Manhattan"},
  {"G21","Queens Plaza","Queens","G21N","Outbound","G21S","Manhattan"},
  {"B06","Roosevelt Island","Manhattan","B06N","Queens","B06S","Downtown"},
  {"F22","Smith-9 Sts","Brooklyn","F22N","Northbound","F22S","Southbound"},
  {"G19","Steinway St","Queens","G19N","Outbound","G19S","Manhattan"},
  {"F04","Sutphin Blvd","Queens","F04N","Jamaica","F04S","Manhattan"},
  {"D20","W 4 St-Wash Sq","Manhattan","D20N","Uptown","D20S","Downtown"},
  {"D42","W 8 St-NY Aquarium","Brooklyn","D42N","Manhattan","D42S","Coney Island"},
  {"G11","Woodhaven Blvd","Queens","G11N","Outbound","G11S","Manhattan"},
  {"F18","York St","Brooklyn","F18N","Manhattan","F18S","Southbound"},
  {"D19","14 St","Manhattan","D19N","Uptown","D19S","Downtown"},
  {"B04","21 St-Queensbridge","Queens","B04N","Outbound","B04S","Manhattan"},
  {"D18","23 St","Manhattan","D18N","Uptown","D18S","Downtown"},
  {"D17","34 St-Herald Sq","Manhattan","D17N","Uptown","D17S","Downtown"},
  {"G20","36 St","Queens","G20N","Outbound","G20S","Manhattan"},
  {"D16","42 St-Bryant Pk","Manhattan","D16N","Uptown","D16S","Downtown"},
  {"G18","46 St","Queens","G18N","Outbound","G18S","Manhattan"},
  {"D15","47-50 Sts-Rockefeller Ctr","Manhattan","D15N","Uptown","D15S","Downtown"},
  {"B10","57 St","Manhattan","B10N","Uptown","B10S","Downtown"},
  {"G10","63 Dr-Rego Park","Queens","G10N","Outbound","G10S","Manhattan"},
  {"G15","65 St","Queens","G15N","Outbound","G15S","Manhattan"},
  {"G09","67 Av","Queens","G09N","Outbound","G09S","Manhattan"},
  {"D21","Broadway-Lafayette St","Manhattan","D21N","Uptown","D21S","Downtown"},
  {"M10","Central Av","Brooklyn","M10N","Inbound","M10S","Middle Village"},
  {"M18","Delancey St-Essex St","Manhattan","M18N","Brooklyn","M18S","Inbound"},
  {"G13","Elmhurst Av","Queens","G13N","Outbound","G13S","Manhattan"},
  {"M12","Flushing Av","Brooklyn","M12N","Outbound","M12S","Manhattan"},
  {"M05","Forest Av","Queens","M05N","Inbound","M05S","Middle Village"},
  {"G08","Forest Hills-71 Av","Queens","G08N","Outbound","G08S","Manhattan"},
  {"M04","Fresh Pond Rd","Queens","M04N","Inbound","M04S","Middle Village"},
  {"G12","Grand Av-Newtown","Queens","G12N","Outbound","G12S","Manhattan"},
  {"M14","Hewes St","Brooklyn","M14N","Outbound","M14S","Manhattan"},
  {"G14","Jackson Hts-Roosevelt Av","Queens","G14N","Outbound","G14S","Manhattan"},
  {"M09","Knickerbocker Av","Brooklyn","M09N","Inbound","M09S","Middle Village"},
  {"B08","Lexington Av/63 St","Manhattan","B08N","Uptown & Queens","B08S","Downtown"},
  {"M13","Lorimer St","Brooklyn","M13N","Outbound","M13S","Manhattan"},
  {"M16","Marcy Av","Brooklyn","M16N","Outbound","M16S","Manhattan"},
  {"M01","Middle Village-Metropolitan Av","Queens","M01N","Inbound","M01S","Middle Village-Metropolitan Av"},
  {"M11","Myrtle Av","Brooklyn","M11N","Outbound","M11S","Manhattan"},
  {"M08","Myrtle-Wyckoff Avs","Brooklyn","M08N","Inbound","M08S","Middle Village"},
  {"G16","Northern Blvd","Queens","G16N","Outbound","G16S","Manhattan"},
  {"B06","Roosevelt Island","Manhattan","B06N","Queens","B06S","Downtown"},
  {"M06","Seneca Av","Queens","M06N","Inbound","M06S","Middle Village"},
  {"G19","Steinway St","Queens","G19N","Outbound","G19S","Manhattan"},
  {"D20","W 4 St-Wash Sq","Manhattan","D20N","Uptown","D20S","Downtown"},
  {"G11","Woodhaven Blvd","Queens","G11N","Outbound","G11S","Manhattan"},
  {"F25","15 St-Prospect Park","Brooklyn","F25N","Northbound","F25S","Southbound"},
  {"G24","21 St","Queens","G24N","Court Square","G24S","Brooklyn"},
  {"F23","4 Av-9 St","Brooklyn","F23N","Northbound","F23S","Southbound"},
  {"F24","7 Av","Brooklyn","F24N","Northbound","F24S","Southbound"},
  {"G33","Bedford-Nostrand Avs","Brooklyn","G33N","Queens","G33S","Southbound"},
  {"F20","Bergen St","Brooklyn","F20N","Northbound","F20S","Southbound"},
  {"G30","Broadway","Brooklyn","G30N","Queens","G30S","Southbound"},
  {"F21","Carroll St","Brooklyn","F21N","Northbound","F21S","Southbound"},
  {"F27","Church Av","Brooklyn","F27N","Northbound","F27S","Southbound"},
  {"G34","Classon Av","Brooklyn","G34N","Queens","G34S","Southbound"},
  {"G35","Clinton-Washington Avs","Brooklyn","G35N","Queens","G35S","Southbound"},
  {"G22","Court Sq","Queens","G22N","Court Sq","G22S","Brooklyn"},
  {"G31","Flushing Av","Brooklyn","G31N","Queens","G31S","Southbound"},
  {"F26","Fort Hamilton Pkwy","Brooklyn","F26N","Northbound","F26S","Southbound"},
  {"G36","Fulton St","Brooklyn","G36N","Queens","G36S","Southbound"},
  {"G26","Greenpoint Av","Brooklyn","G26N","Queens","G26S","Southbound"},
  {"A42","Hoyt-Schermerhorn Sts","Brooklyn","A42N","Westbound","A42S","Queens"},
  {"G29","Metropolitan Av","Brooklyn","G29N","Queens","G29S","Southbound"},
  {"G32","Myrtle-Willoughby Avs","Brooklyn","G32N","Queens","G32S","Southbound"},
  {"G28","Nassau Av","Brooklyn","G28N","Queens","G28S","Southbound"},
  {"F22","Smith-9 Sts","Brooklyn","F22N","Northbound","F22S","Southbound"},
  {"J14","104 St","Queens","J14N","Jamaica","J14S","Manhattan"},
  {"J13","111 St","Queens","J13N","Jamaica","J13S","Manhattan"},
  {"J12","121 St","Queens","J12N","Jamaica","J12S","Manhattan"},
  {"J17","75 St-Elderts Ln","Queens","J17N","Jamaica","J17S","Manhattan"},
  {"J16","85 St-Forest Pkwy","Queens","J16N","Jamaica","J16S","Manhattan"},
  {"J24","Alabama Av","Brooklyn","J24N","Outbound","J24S","Manhattan"},
  {"M19","Bowery","Manhattan","M19N","Brooklyn","M19S","Downtown"},
  {"M23","Broad St","Manhattan","M23N","Brooklyn","M23S","Broad St"},
  {"J27","Broadway Junction","Brooklyn","J27N","Outbound","J27S","Manhattan"},
  {"M20","Canal St","Manhattan","M20N","Brooklyn","M20S","Downtown"},
  {"M21","Chambers St","Manhattan","M21N","Brooklyn","M21S","Downtown"},
  {"J28","Chauncey St","Brooklyn","J28N","Outbound","J28S","Manhattan"},
  {"J22","Cleveland St","Brooklyn","J22N","Outbound","J22S","Manhattan"},
  {"J20","Crescent St","Brooklyn","J20N","Outbound","J20S","Manhattan"},
  {"J19","Cypress Hills","Brooklyn","J19N","Queens","J19S","Manhattan"},
  {"M18","Delancey St-Essex St","Manhattan","M18N","Brooklyn","M18S","Inbound"},
  {"M12","Flushing Av","Brooklyn","M12N","Outbound","M12S","Manhattan"},
  {"M22","Fulton St","Manhattan","M22N","Brooklyn","M22S","Downtown"},
  {"J30","Gates Av","Brooklyn","J30N","Outbound","J30S","Manhattan"},
  {"J29","Halsey St","Brooklyn","J29N","Outbound","J29S","Manhattan"},
  {"M14","Hewes St","Brooklyn","M14N","Outbound","M14S","Manhattan"},
  {"G05","Jamaica Center-Parsons/Archer","Queens","G05N","Jamaica Center-Parsons/Archer","G05S","Manhattan"},
  {"J31","Kosciuszko St","Brooklyn","J31N","Outbound","J31S","Manhattan"},
  {"M13","Lorimer St","Brooklyn","M13N","Outbound","M13S","Manhattan"},
  {"M16","Marcy Av","Brooklyn","M16N","Outbound","M16S","Manhattan"},
  {"M11","Myrtle Av","Brooklyn","M11N","Outbound","M11S","Manhattan"},
  {"J21","Norwood Av","Brooklyn","J21N","Outbound","J21S","Manhattan"},
  {"G06","Sutphin Blvd-Archer Av-JFK Airport","Queens","G06N","Jamaica","G06S","Manhattan"},
  {"J23","Van Siclen Av","Brooklyn","J23N","Outbound","J23S","Manhattan"},
  {"J15","Woodhaven Blvd","Queens","J15N","Jamaica","J15S","Manhattan"},
  {"J14","104 St","Queens","J14N","Jamaica","J14S","Manhattan"},
  {"J12","121 St","Queens","J12N","Jamaica","J12S","Manhattan"},
  {"J17","75 St-Elderts Ln","Queens","J17N","Jamaica","J17S","Manhattan"},
  {"J24","Alabama Av","Brooklyn","J24N","Outbound","J24S","Manhattan"},
  {"M19","Bowery","Manhattan","M19N","Brooklyn","M19S","Downtown"},
  {"M23","Broad St","Manhattan","M23N","Brooklyn","M23S","Broad St"},
  {"J27","Broadway Junction","Brooklyn","J27N","Outbound","J27S","Manhattan"},
  {"M20","Canal St","Manhattan","M20N","Brooklyn","M20S","Downtown"},
  {"M21","Chambers St","Manhattan","M21N","Brooklyn","M21S","Downtown"},
  {"J28","Chauncey St","Brooklyn","J28N","Outbound","J28S","Manhattan"},
  {"J20","Crescent St","Brooklyn","J20N","Outbound","J20S","Manhattan"},
  {"M18","Delancey St-Essex St","Manhattan","M18N","Brooklyn","M18S","Inbound"},
  {"M22","Fulton St","Manhattan","M22N","Brooklyn","M22S","Downtown"},
  {"J30","Gates Av","Brooklyn","J30N","Outbound","J30S","Manhattan"},
  {"G05","Jamaica Center-Parsons/Archer","Queens","G05N","Jamaica Center-Parsons/Archer","G05S","Manhattan"},
  {"M16","Marcy Av","Brooklyn","M16N","Outbound","M16S","Manhattan"},
  {"M11","Myrtle Av","Brooklyn","M11N","Outbound","M11S","Manhattan"},
  {"J21","Norwood Av","Brooklyn","J21N","Outbound","J21S","Manhattan"},
  {"G06","Sutphin Blvd-Archer Av-JFK Airport","Queens","G06N","Jamaica","G06S","Manhattan"},
  {"J23","Van Siclen Av","Brooklyn","J23N","Outbound","J23S","Manhattan"},
  {"J15","Woodhaven Blvd","Queens","J15N","Jamaica","J15S","Manhattan"},
  {"L06","1 Av","Manhattan","L06N","West Side","L06S","Brooklyn"},
  {"L03","14 St-Union Sq","Manhattan","L03N","West Side","L03S","Brooklyn"},
  {"L05","3 Av","Manhattan","L05N","West Side","L05S","Brooklyn"},
  {"L02","6 Av","Manhattan","L02N","West Side","L02S","Brooklyn"},
  {"L01","8 Av","Manhattan","L01N","8 Av","L01S","Brooklyn"},
  {"L24","Atlantic Av","Brooklyn","L24N","Manhattan","L24S","Canarsie"},
  {"L08","Bedford Av","Brooklyn","L08N","Manhattan","L08S","Outbound"},
  {"L22","Broadway Junction","Brooklyn","L22N","Manhattan","L22S","Outbound"},
  {"L21","Bushwick Av-Aberdeen St","Brooklyn","L21N","Manhattan","L21S","Outbound"},
  {"L29","Canarsie-Rockaway Pkwy","Brooklyn","L29N","Manhattan","L29S","Canarsie-Rockaway Pkwy"},
  {"L16","DeKalb Av","Brooklyn","L16N","Manhattan","L16S","Outbound"},
  {"L28","East 105 St","Brooklyn","L28N","Manhattan","L28S","Canarsie"},
  {"L11","Graham Av","Brooklyn","L11N","Manhattan","L11S","Outbound"},
  {"L12","Grand St","Brooklyn","L12N","Manhattan","L12S","Outbound"},
  {"L19","Halsey St","Queens","L19N","Manhattan","L19S","Outbound"},
  {"L15","Jefferson St","Brooklyn","L15N","Manhattan","L15S","Outbound"},
  {"L26","Livonia Av","Brooklyn","L26N","Manhattan","L26S","Canarsie"},
  {"L10","Lorimer St","Brooklyn","L10N","Manhattan","L10S","Outbound"},
  {"L13","Montrose Av","Brooklyn","L13N","Manhattan","L13S","Outbound"},
  {"L14","Morgan Av","Brooklyn","L14N","Manhattan","L14S","Outbound"},
  {"L17","Myrtle-Wyckoff Avs","Brooklyn","L17N","Manhattan","L17S","Outbound"},
  {"L27","New Lots Av","Brooklyn","L27N","Manhattan","L27S","Canarsie"},
  {"L25","Sutter Av","Brooklyn","L25N","Manhattan","L25S","Canarsie"},
  {"L20","Wilson Av","Brooklyn","L20N","Manhattan","L20S","Outbound"},
  {"R20","14 St-Union Sq","Manhattan","R20N","Uptown","R20S","Downtown"},
  {"N05","18 Av","Brooklyn","N05N","Manhattan","N05S","Coney Island"},
  {"N06","20 Av","Brooklyn","N06N","Manhattan","N06S","Coney Island"},
  {"R19","23 St","Manhattan","R19N","Uptown","R19S","Downtown"},
  {"R35","25 St","Brooklyn","R35N","Manhattan","R35S","Southbound"},
  {"R18","28 St","Manhattan","R18N","Uptown","R18S","Downtown"},
  {"R04","30 Av","Queens","R04N","Astoria","R04S","Manhattan"},
  {"R17","34 St-Herald Sq","Manhattan","R17N","Uptown","R17S","Downtown"},
  {"R06","36 Av","Queens","R06N","Astoria","R06S","Manhattan"},
  {"R36","36 St","Brooklyn","R36N","Manhattan","R36S","Southbound"},
  {"R08","39 Av-Dutch Kills","Queens","R08N","Astoria","R08S","Manhattan"},
  {"R33","4 Av-9 St","Brooklyn","R33N","Manhattan","R33S","Southbound"},
  {"R39","45 St","Brooklyn","R39N","Manhattan","R39S","Southbound"},
  {"R15","49 St","Manhattan","R15N","Uptown","R15S","Downtown"},
  {"R13","5 Av/59 St","Manhattan","R13N","Queens","R13S","Downtown"},
  {"R40","53 St","Brooklyn","R40N","Manhattan","R40S","Southbound"},
  {"R14","57 St-7 Av","Manhattan","R14N","Uptown","R14S","Downtown"},
  {"R41","59 St","Brooklyn","R41N","Manhattan","R41S","Southbound"},
  {"Q03","72 St","Manhattan","Q03N","Uptown","Q03S","Downtown"},
  {"N02","8 Av","Brooklyn","N02N","Manhattan","N02S","Coney Island"},
  {"R21","8 St-NYU","Manhattan","R21N","Uptown","R21S","Downtown"},
  {"N10","86 St","Brooklyn","N10N","Manhattan","N10S","Coney Island"},
  {"Q04","86 St","Manhattan","Q04N","Uptown","Q04S","Downtown"},
  {"Q05","96 St","Manhattan","Q05N","96 St","Q05S","Downtown"},
  {"R03","Astoria Blvd","Queens","R03N","Astoria","R03S","Manhattan"},
  {"R01","Astoria-Ditmars Blvd","Queens","R01N","Astoria-Ditmars Blvd","R01S","Manhattan"},
  {"R31","Atlantic Av-Barclays Ctr","Brooklyn","R31N","Manhattan","R31S","Southbound"},
  {"N09","Avenue U","Brooklyn","N09N","Manhattan","N09S","Coney Island"},
  {"N07","Bay Pkwy","Brooklyn","N07N","Manhattan","N07S","Coney Island"},
  {"R05","Broadway","Queens","R05N","Astoria","R05S","Manhattan"},
  {"Q01","Canal St","Manhattan","Q01N","Uptown","Q01S","Downtown"},
  {"R23","Canal St","Manhattan","R23N","Uptown","R23S","Downtown"},
  {"R24","City Hall","Manhattan","R24N","Uptown","R24S","Downtown"},
  {"D43","Coney Island-Stillwell Av","Brooklyn","D43N","Manhattan","D43S","Coney Island-Stillwell Av"},
  {"R25","Cortlandt St","Manhattan","R25N","Uptown","R25S","Downtown"},
  {"R28","Court St","Brooklyn","R28N","Manhattan","R28S","Southbound"},
  {"R30","DeKalb Av","Brooklyn","R30N","Manhattan","R30S","Southbound"},
  {"N03","Fort Hamilton Pkwy","Brooklyn","N03N","Manhattan","N03S","Coney Island"},
  {"R29","Jay St-MetroTech","Brooklyn","R29N","Manhattan","R29S","Southbound"},
  {"N08","Kings Hwy","Brooklyn","N08N","Manhattan","N08S","Coney Island"},
  {"R11","Lexington Av/59 St","Manhattan","R11N","Queens","R11S","Downtown"},
  {"B08","Lexington Av/63 St","Manhattan","B08N","Uptown & Queens","B08S","Downtown"},
  {"N04","New Utrecht Av","Brooklyn","N04N","Manhattan","N04S","Coney Island"},
  {"R22","Prince St","Manhattan","R22N","Uptown","R22S","Downtown"},
  {"R34","Prospect Av","Brooklyn","R34N","Manhattan","R34S","Southbound"},
  {"R09","Queensboro Plaza","Queens","R09N","Astoria","R09S","Manhattan"},
  {"R26","Rector St","Manhattan","R26N","Uptown","R26S","Downtown"},
  {"R16","Times Sq-42 St","Manhattan","R16N","Uptown","R16S","Downtown"},
  {"R32","Union St","Brooklyn","R32N","Manhattan","R32S","Southbound"},
  {"R27","Whitehall St-South Ferry","Manhattan","R27N","Uptown","R27S","Downtown"},
  {"R20","14 St-Union Sq","Manhattan","R20N","Uptown","R20S","Downtown"},
  {"R19","23 St","Manhattan","R19N","Uptown","R19S","Downtown"},
  {"R18","28 St","Manhattan","R18N","Uptown","R18S","Downtown"},
  {"R17","34 St-Herald Sq","Manhattan","R17N","Uptown","R17S","Downtown"},
  {"R15","49 St","Manhattan","R15N","Uptown","R15S","Downtown"},
  {"R14","57 St-7 Av","Manhattan","R14N","Uptown","R14S","Downtown"},
  {"D25","7 Av","Brooklyn","D25N","Manhattan","D25S","Southbound"},
  {"Q03","72 St","Manhattan","Q03N","Uptown","Q03S","Downtown"},
  {"R21","8 St-NYU","Manhattan","R21N","Uptown","R21S","Downtown"},
  {"Q04","86 St","Manhattan","Q04N","Uptown","Q04S","Downtown"},
  {"Q05","96 St","Manhattan","Q05N","96 St","Q05S","Downtown"},
  {"D24","Atlantic Av-Barclays Ctr","Brooklyn","D24N","Manhattan","D24S","Southbound"},
  {"D32","Avenue H","Brooklyn","D32N","Manhattan","D32S","Southbound"},
  {"D33","Avenue J","Brooklyn","D33N","Manhattan","D33S","Southbound"},
  {"D34","Avenue M","Brooklyn","D34N","Manhattan","D34S","Southbound"},
  {"D37","Avenue U","Brooklyn","D37N","Manhattan","D37S","Southbound"},
  {"D29","Beverley Rd","Brooklyn","D29N","Manhattan","D29S","Southbound"},
  {"D40","Brighton Beach","Brooklyn","D40N","Manhattan","D40S","Southbound"},
  {"Q01","Canal St","Manhattan","Q01N","Uptown","Q01S","Downtown"},
  {"D28","Church Av","Brooklyn","D28N","Manhattan","D28S","Southbound"},
  {"D43","Coney Island-Stillwell Av","Brooklyn","D43N","Manhattan","D43S","Coney Island-Stillwell Av"},
  {"D30","Cortelyou Rd","Brooklyn","D30N","Manhattan","D30S","Southbound"},
  {"R30","DeKalb Av","Brooklyn","R30N","Manhattan","R30S","Southbound"},
  {"D35","Kings Hwy","Brooklyn","D35N","Manhattan","D35S","Southbound"},
  {"B08","Lexington Av/63 St","Manhattan","B08N","Uptown & Queens","B08S","Downtown"},
  {"D38","Neck Rd","Brooklyn","D38N","Manhattan","D38S","Southbound"},
  {"D31","Newkirk Plaza","Brooklyn","D31N","Manhattan","D31S","Southbound"},
  {"D41","Ocean Pkwy","Brooklyn","D41N","Manhattan","D41S","Coney Island"},
  {"D27","Parkside Av","Brooklyn","D27N","Manhattan","D27S","Southbound"},
  {"R22","Prince St","Manhattan","R22N","Uptown","R22S","Downtown"},
  {"D26","Prospect Park","Brooklyn","D26N","Northbound","D26S","Southbound"},
  {"D39","Sheepshead Bay","Brooklyn","D39N","Manhattan","D39S","Southbound"},
  {"R16","Times Sq-42 St","Manhattan","R16N","Uptown","R16S","Downtown"},
  {"D42","W 8 St-NY Aquarium","Brooklyn","D42N","Manhattan","D42S","Coney Island"},
  {"R20","14 St-Union Sq","Manhattan","R20N","Uptown","R20S","Downtown"},
  {"R19","23 St","Manhattan","R19N","Uptown","R19S","Downtown"},
  {"R35","25 St","Brooklyn","R35N","Manhattan","R35S","Southbound"},
  {"R18","28 St","Manhattan","R18N","Uptown","R18S","Downtown"},
  {"R17","34 St-Herald Sq","Manhattan","R17N","Uptown","R17S","Downtown"},
  {"G20","36 St","Queens","G20N","Outbound","G20S","Manhattan"},
  {"R36","36 St","Brooklyn","R36N","Manhattan","R36S","Southbound"},
  {"R33","4 Av-9 St","Brooklyn","R33N","Manhattan","R33S","Southbound"},
  {"R39","45 St","Brooklyn","R39N","Manhattan","R39S","Southbound"},
  {"G18","46 St","Queens","G18N","Outbound","G18S","Manhattan"},
  {"R15","49 St","Manhattan","R15N","Uptown","R15S","Downtown"},
  {"R13","5 Av/59 St","Manhattan","R13N","Queens","R13S","Downtown"},
  {"R40","53 St","Brooklyn","R40N","Manhattan","R40S","Southbound"},
  {"R14","57 St-7 Av","Manhattan","R14N","Uptown","R14S","Downtown"},
  {"R41","59 St","Brooklyn","R41N","Manhattan","R41S","Southbound"},
  {"B16","62 St","Brooklyn","B16N","Manhattan","B16S","Southbound"},
  {"G10","63 Dr-Rego Park","Queens","G10N","Outbound","G10S","Manhattan"},
  {"G15","65 St","Queens","G15N","Outbound","G15S","Manhattan"},
  {"G09","67 Av","Queens","G09N","Outbound","G09S","Manhattan"},
  {"Q03","72 St","Manhattan","Q03N","Uptown","Q03S","Downtown"},
  {"R43","77 St","Brooklyn","R43N","Manhattan","R43S","Bay Ridge"},
  {"R21","8 St-NYU","Manhattan","R21N","Uptown","R21S","Downtown"},
  {"Q04","86 St","Manhattan","Q04N","Uptown","Q04S","Downtown"},
  {"R44","86 St","Brooklyn","R44N","Manhattan","R44S","Bay Ridge"},
  {"B12","9 Av","Brooklyn","B12N","Manhattan","B12S","Southbound"},
  {"Q05","96 St","Manhattan","Q05N","96 St","Q05S","Downtown"},
  {"R31","Atlantic Av-Barclays Ctr","Brooklyn","R31N","Manhattan","R31S","Southbound"},
  {"B21","Bay Pkwy","Brooklyn","B21N","Manhattan","B21S","Southbound"},
  {"R42","Bay Ridge Av","Brooklyn","R42N","Manhattan","R42S","Bay Ridge"},
  {"R45","Bay Ridge-95 St","Brooklyn","R45N","Manhattan","R45S","Bay Ridge-95 St"},
  {"R23","Canal St","Manhattan","R23N","Uptown","R23S","Downtown"},
  {"R24","City Hall","Manhattan","R24N","Uptown","R24S","Downtown"},
  {"R25","Cortlandt St","Manhattan","R25N","Uptown","R25S","Downtown"},
  {"R28","Court St","Brooklyn","R28N","Manhattan","R28S","Southbound"},
  {"R30","DeKalb Av","Brooklyn","R30N","Manhattan","R30S","Southbound"},
  {"G13","Elmhurst Av","Queens","G13N","Outbound","G13S","Manhattan"},
  {"G08","Forest Hills-71 Av","Queens","G08N","Outbound","G08S","Manhattan"},
  {"G12","Grand Av-Newtown","Queens","G12N","Outbound","G12S","Manhattan"},
  {"G14","Jackson Hts-Roosevelt Av","Queens","G14N","Outbound","G14S","Manhattan"},
  {"R29","Jay St-MetroTech","Brooklyn","R29N","Manhattan","R29S","Southbound"},
  {"R11","Lexington Av/59 St","Manhattan","R11N","Queens","R11S","Downtown"},
  {"B08","Lexington Av/63 St","Manhattan","B08N","Uptown & Queens","B08S","Downtown"},
  {"G16","Northern Blvd","Queens","G16N","Outbound","G16S","Manhattan"},
  {"R22","Prince St","Manhattan","R22N","Uptown","R22S","Downtown"},
  {"R34","Prospect Av","Brooklyn","R34N","Manhattan","R34S","Southbound"},
  {"G21","Queens Plaza","Queens","G21N","Outbound","G21S","Manhattan"},
  {"R26","Rector St","Manhattan","R26N","Uptown","R26S","Downtown"},
  {"G19","Steinway St","Queens","G19N","Outbound","G19S","Manhattan"},
  {"R16","Times Sq-42 St","Manhattan","R16N","Uptown","R16S","Downtown"},
  {"R32","Union St","Brooklyn","R32N","Manhattan","R32S","Southbound"},
  {"R27","Whitehall St-South Ferry","Manhattan","R27N","Uptown","R27S","Downtown"},
  {"G11","Woodhaven Blvd","Queens","G11N","Outbound","G11S","Manhattan"},
  {"R20","14 St-Union Sq","Manhattan","R20N","Uptown","R20S","Downtown"},
  {"N05","18 Av","Brooklyn","N05N","Manhattan","N05S","Coney Island"},
  {"N06","20 Av","Brooklyn","N06N","Manhattan","N06S","Coney Island"},
  {"R19","23 St","Manhattan","R19N","Uptown","R19S","Downtown"},
  {"R35","25 St","Brooklyn","R35N","Manhattan","R35S","Southbound"},
  {"R18","28 St","Manhattan","R18N","Uptown","R18S","Downtown"},
  {"R04","30 Av","Queens","R04N","Astoria","R04S","Manhattan"},
  {"R17","34 St-Herald Sq","Manhattan","R17N","Uptown","R17S","Downtown"},
  {"R06","36 Av","Queens","R06N","Astoria","R06S","Manhattan"},
  {"R36","36 St","Brooklyn","R36N","Manhattan","R36S","Southbound"},
  {"R08","39 Av-Dutch Kills","Queens","R08N","Astoria","R08S","Manhattan"},
  {"R33","4 Av-9 St","Brooklyn","R33N","Manhattan","R33S","Southbound"},
  {"R39","45 St","Brooklyn","R39N","Manhattan","R39S","Southbound"},
  {"R15","49 St","Manhattan","R15N","Uptown","R15S","Downtown"},
  {"R13","5 Av/59 St","Manhattan","R13N","Queens","R13S","Downtown"},
  {"R40","53 St","Brooklyn","R40N","Manhattan","R40S","Southbound"},
  {"R14","57 St-7 Av","Manhattan","R14N","Uptown","R14S","Downtown"},
  {"R41","59 St","Brooklyn","R41N","Manhattan","R41S","Southbound"},
  {"B16","62 St","Brooklyn","B16N","Manhattan","B16S","Southbound"},
  {"N02","8 Av","Brooklyn","N02N","Manhattan","N02S","Coney Island"},
  {"R21","8 St-NYU","Manhattan","R21N","Uptown","R21S","Downtown"},
  {"N10","86 St","Brooklyn","N10N","Manhattan","N10S","Coney Island"},
  {"B12","9 Av","Brooklyn","B12N","Manhattan","B12S","Southbound"},
  {"R03","Astoria Blvd","Queens","R03N","Astoria","R03S","Manhattan"},
  {"R01","Astoria-Ditmars Blvd","Queens","R01N","Astoria-Ditmars Blvd","R01S","Manhattan"},
  {"R31","Atlantic Av-Barclays Ctr","Brooklyn","R31N","Manhattan","R31S","Southbound"},
  {"N09","Avenue U","Brooklyn","N09N","Manhattan","N09S","Coney Island"},
  {"B21","Bay Pkwy","Brooklyn","B21N","Manhattan","B21S","Southbound"},
  {"N07","Bay Pkwy","Brooklyn","N07N","Manhattan","N07S","Coney Island"},
  {"R05","Broadway","Queens","R05N","Astoria","R05S","Manhattan"},
  {"R23","Canal St","Manhattan","R23N","Uptown","R23S","Downtown"},
  {"R24","City Hall","Manhattan","R24N","Uptown","R24S","Downtown"},
  {"R25","Cortlandt St","Manhattan","R25N","Uptown","R25S","Downtown"},
  {"R28","Court St","Brooklyn","R28N","Manhattan","R28S","Southbound"},
  {"R30","DeKalb Av","Brooklyn","R30N","Manhattan","R30S","Southbound"},
  {"N03","Fort Hamilton Pkwy","Brooklyn","N03N","Manhattan","N03S","Coney Island"},
  {"R29","Jay St-MetroTech","Brooklyn","R29N","Manhattan","R29S","Southbound"},
  {"N08","Kings Hwy","Brooklyn","N08N","Manhattan","N08S","Coney Island"},
  {"R11","Lexington Av/59 St","Manhattan","R11N","Queens","R11S","Downtown"},
  {"N04","New Utrecht Av","Brooklyn","N04N","Manhattan","N04S","Coney Island"},
  {"R22","Prince St","Manhattan","R22N","Uptown","R22S","Downtown"},
  {"R34","Prospect Av","Brooklyn","R34N","Manhattan","R34S","Southbound"},
  {"R09","Queensboro Plaza","Queens","R09N","Astoria","R09S","Manhattan"},
  {"R26","Rector St","Manhattan","R26N","Uptown","R26S","Downtown"},
  {"R16","Times Sq-42 St","Manhattan","R16N","Uptown","R16S","Downtown"},
  {"R32","Union St","Brooklyn","R32N","Manhattan","R32S","Southbound"},
  {"R27","Whitehall St-South Ferry","Manhattan","R27N","Uptown","R27S","Downtown"},
  {"901","Grand Central-42 St","Manhattan","901N","Times Square","901S","Grand Central-42 St"},
  {"902","Times Sq-42 St","Manhattan","902N","Times Sq-42 St","902S","Grand Central"},
  {"S04","Botanic Garden","Brooklyn","S04N","Franklin Av","S04S","Prospect Park"},
  {"S01","Franklin Av","Brooklyn","S01N","Franklin Av","S01S","Prospect Park"},
  {"S03","Park Pl","Brooklyn","S03N","Franklin Av","S03S","Prospect Park"},
  {"D26","Prospect Park","Brooklyn","D26N","Northbound","D26S","Southbound"},
  {"H01","Aqueduct Racetrack","Queens","H01N","Manhattan","H01S","Rockaways"},
  {"H02","Aqueduct-N Conduit Av","Queens","H02N","Manhattan","H02S","Rockaways"},
  {"H14","Beach 105 St","Queens","H14N","Inbound","H14S","Rockaway Park"},
  {"H12","Beach 90 St","Queens","H12N","Inbound","H12S","Rockaway Park"},
  {"H13","Beach 98 St","Queens","H13N","Inbound","H13S","Rockaway Park"},
  {"H04","Broad Channel","Queens","H04N","Inbound","H04S","Rockaways"},
  {"H03","Howard Beach-JFK Airport","Queens","H03N","Manhattan","H03S","Rockaways"},
  {"A61","Rockaway Blvd","Queens","A61N","Manhattan","A61S","Outbound"},
  {"H15","Rockaway Park-Beach 116 St","Queens","H15N","Inbound","H15S","Rockaway Park-Beach 116 St"},
  {"S17","Annadale","Staten Island","S17N","Ferry","S17S","South Shore"},
  {"S11","Arthur Kill","Staten Island","S11N","Ferry","S11S","Tottenville"},
  {"S20","Bay Terrace","Staten Island","S20N","Ferry","S20S","South Shore"},
  {"S28","Clifton","Staten Island","S28N","Ferry","S28S","South Shore"},
  {"S25","Dongan Hills","Staten Island","S25N","Ferry","S25S","South Shore"},
  {"S18","Eltingville","Staten Island","S18N","Ferry","S18S","South Shore"},
  {"S23","Grant City","Staten Island","S23N","Ferry","S23S","South Shore"},
  {"S27","Grasmere","Staten Island","S27N","Ferry","S27S","South Shore"},
  {"S19","Great Kills","Staten Island","S19N","Ferry","S19S","South Shore"},
  {"S16","Huguenot","Staten Island","S16N","Ferry","S16S","South Shore"},
  {"S24","Jefferson Av","Staten Island","S24N","Ferry","S24S","South Shore"},
  {"S22","New Dorp","Staten Island","S22N","Ferry","S22S","South Shore"},
  {"S21","Oakwood Heights","Staten Island","S21N","Ferry","S21S","South Shore"},
  {"S26","Old Town","Staten Island","S26N","Ferry","S26S","South Shore"},
  {"S14","Pleasant Plains","Staten Island","S14N","Ferry","S14S","South Shore"},
  {"S15","Prince's Bay","Staten Island","S15N","Ferry","S15S","South Shore"},
  {"S13","Richmond Valley","Staten Island","S13N","Ferry","S13S","Tottenville"},
  {"S31","St George","Staten Island","S31N","St George","S31S","South Shore"},
  {"S29","Stapleton","Staten Island","S29N","Ferry","S29S","South Shore"},
  {"S30","Tompkinsville","Staten Island","S30N","Ferry","S30S","South Shore"},
  {"S09","Tottenville","Staten Island","S09N","Ferry","S09S","Tottenville"},
};

static const RouteDef ROUTES[] = {
  {"1","1","1 train","https://api-endpoint.mta.info/Dataservice/mtagtfsfeeds/nyct%2Fgtfs","1",0,38},
  {"2","2","2 train","https://api-endpoint.mta.info/Dataservice/mtagtfsfeeds/nyct%2Fgtfs","2",38,71},
  {"3","3","3 train","https://api-endpoint.mta.info/Dataservice/mtagtfsfeeds/nyct%2Fgtfs","3",109,34},
  {"4","4","4 train","https://api-endpoint.mta.info/Dataservice/mtagtfsfeeds/nyct%2Fgtfs","4",143,54},
  {"5","5","5 train","https://api-endpoint.mta.info/Dataservice/mtagtfsfeeds/nyct%2Fgtfs","5",197,55},
  {"6","6","6 train","https://api-endpoint.mta.info/Dataservice/mtagtfsfeeds/nyct%2Fgtfs","6,6X",252,38},
  {"7","7","7 train","https://api-endpoint.mta.info/Dataservice/mtagtfsfeeds/nyct%2Fgtfs","7,7X",290,22},
  {"A","A","A train","https://api-endpoint.mta.info/Dataservice/mtagtfsfeeds/nyct%2Fgtfs-ace","A",312,66},
  {"C","C","C train","https://api-endpoint.mta.info/Dataservice/mtagtfsfeeds/nyct%2Fgtfs-ace","C",378,40},
  {"E","E","E train","https://api-endpoint.mta.info/Dataservice/mtagtfsfeeds/nyct%2Fgtfs-ace","E",418,36},
  {"B","B","B train","https://api-endpoint.mta.info/Dataservice/mtagtfsfeeds/nyct%2Fgtfs-bdfm","B",454,37},
  {"D","D","D train","https://api-endpoint.mta.info/Dataservice/mtagtfsfeeds/nyct%2Fgtfs-bdfm","D",491,41},
  {"F","F","F train","https://api-endpoint.mta.info/Dataservice/mtagtfsfeeds/nyct%2Fgtfs-bdfm","F,FX",532,59},
  {"M","M","M train","https://api-endpoint.mta.info/Dataservice/mtagtfsfeeds/nyct%2Fgtfs-bdfm","M",591,36},
  {"G","G","G train","https://api-endpoint.mta.info/Dataservice/mtagtfsfeeds/nyct%2Fgtfs-g","G",627,21},
  {"J","J","J train","https://api-endpoint.mta.info/Dataservice/mtagtfsfeeds/nyct%2Fgtfs-jz","J",648,30},
  {"Z","Z","Z train","https://api-endpoint.mta.info/Dataservice/mtagtfsfeeds/nyct%2Fgtfs-jz","Z",678,21},
  {"L","L","L train","https://api-endpoint.mta.info/Dataservice/mtagtfsfeeds/nyct%2Fgtfs-l","L",699,24},
  {"N","N","N train","https://api-endpoint.mta.info/Dataservice/mtagtfsfeeds/nyct%2Fgtfs-nqrw","N",723,50},
  {"Q","Q","Q train","https://api-endpoint.mta.info/Dataservice/mtagtfsfeeds/nyct%2Fgtfs-nqrw","Q",773,34},
  {"R","R","R train","https://api-endpoint.mta.info/Dataservice/mtagtfsfeeds/nyct%2Fgtfs-nqrw","R",807,52},
  {"W","W","W train","https://api-endpoint.mta.info/Dataservice/mtagtfsfeeds/nyct%2Fgtfs-nqrw","W",859,47},
  {"GS","S","42 St Shuttle","https://api-endpoint.mta.info/Dataservice/mtagtfsfeeds/nyct%2Fgtfs","GS",906,2},
  {"FS","S","Franklin Av Shuttle","https://api-endpoint.mta.info/Dataservice/mtagtfsfeeds/nyct%2Fgtfs-bdfm","FS",908,4},
  {"H","S","Rockaway Park Shuttle","https://api-endpoint.mta.info/Dataservice/mtagtfsfeeds/nyct%2Fgtfs-ace","H",912,9},
  {"SI","SIR","Staten Island Railway","https://api-endpoint.mta.info/Dataservice/mtagtfsfeeds/nyct%2Fgtfs-si","SI",921,21},
};

constexpr size_t ROUTE_COUNT = sizeof(ROUTES) / sizeof(ROUTES[0]);
constexpr size_t STATION_COUNT = sizeof(STATIONS) / sizeof(STATIONS[0]);
inline const RouteDef *findRoute(const String &id) { for (size_t i=0;i<ROUTE_COUNT;++i) if (id == ROUTES[i].id) return &ROUTES[i]; return nullptr; }
inline const StationDef *findStation(const RouteDef &route, const String &id) { for (uint16_t i=0;i<route.stationCount;++i) { const StationDef &station=STATIONS[route.stationStart+i]; if (id == station.id) return &station; } return nullptr; }
}  // namespace SubwayCatalog
