AloeVeraZ/TrainUI/Train UI Mini/TrainUIMiniCode/TrainUIMiniCode.ino

/*
  Train UI Mini for the Elecrow CrowPanel ESP32-S3 2.13-inch e-paper display.

  Arduino IDE opens this sketch and compiles the .cpp files beside it.
  Easy Wi-Fi defaults live in UserConfig.h. Train and station are selected
  from the board's setup webpage on first boot.
*/
